mkulesh/stm32WindowSensor/images/screenschots/floor_1_alarm.png

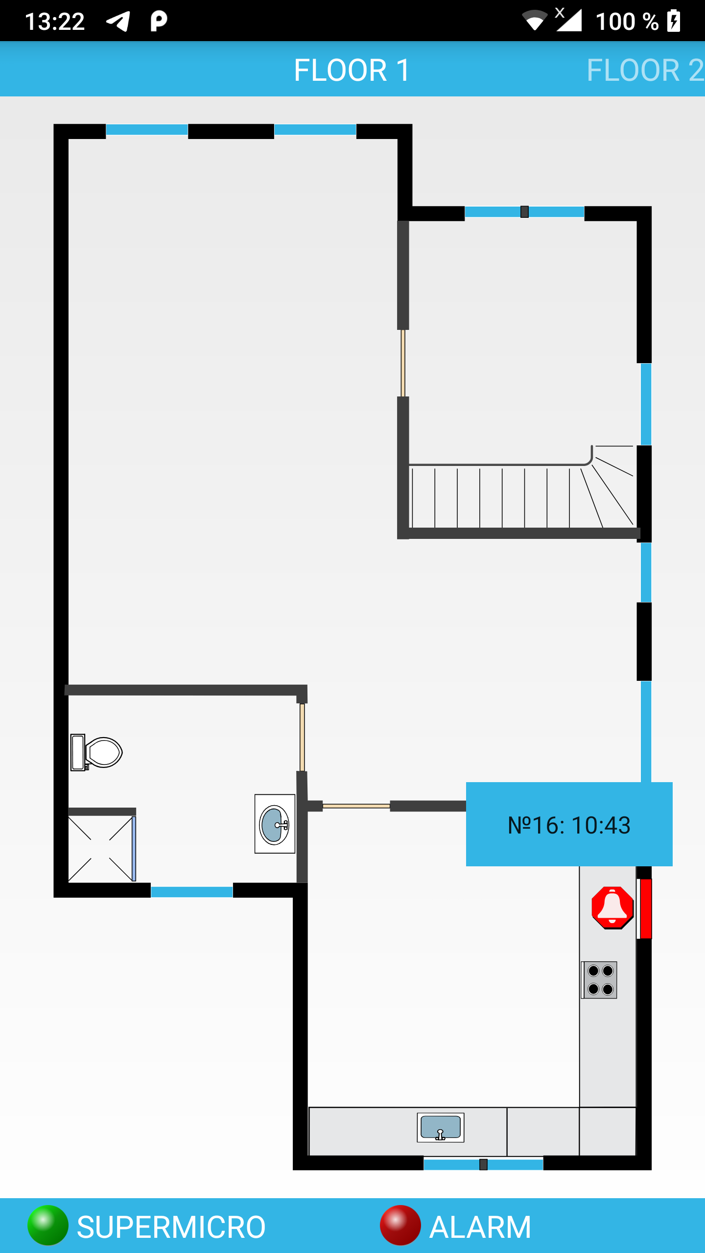
images/screenschots/floor_1_alarm.png
