mkulesh/stm32WindowSensor/images/screenschots/server.png

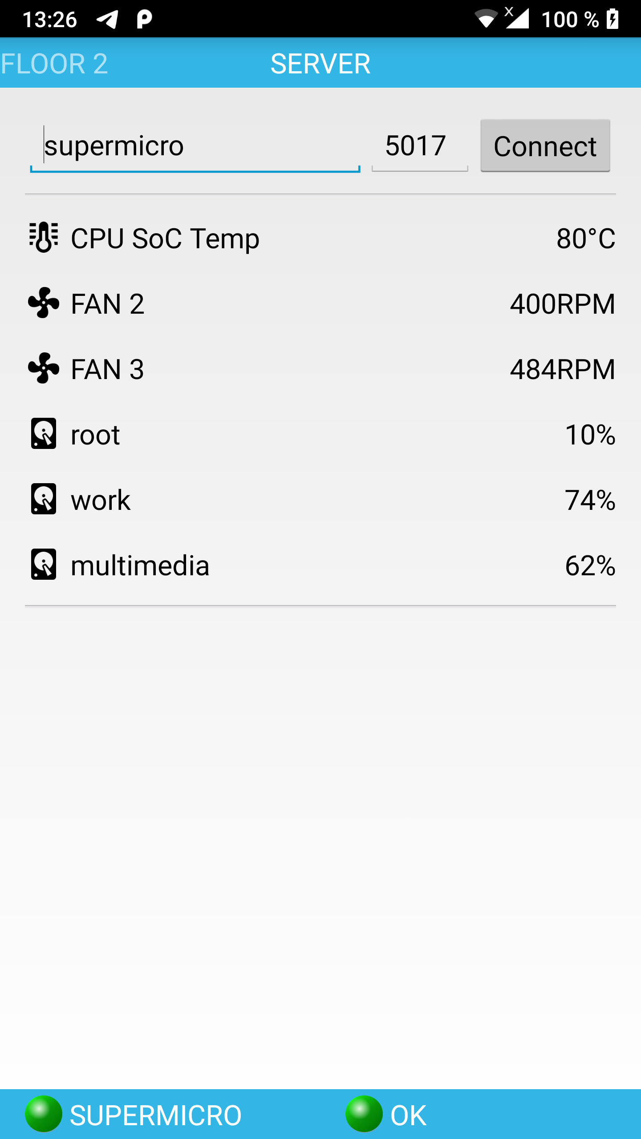
images/screenschots/server.png
