mkulesh/stm32WindowSensor/images/sensors/sensor06.jpg

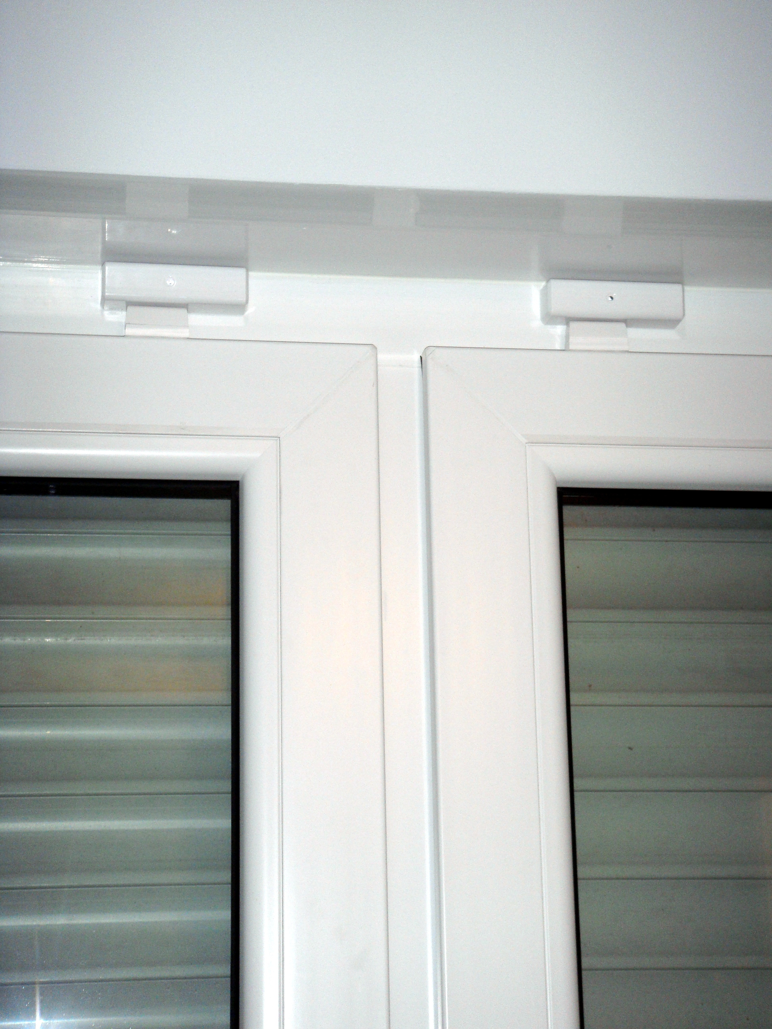
images/sensors/sensor06.jpg
