mkulesh/stm32WindowSensor/images/sensors/sensor08.jpg

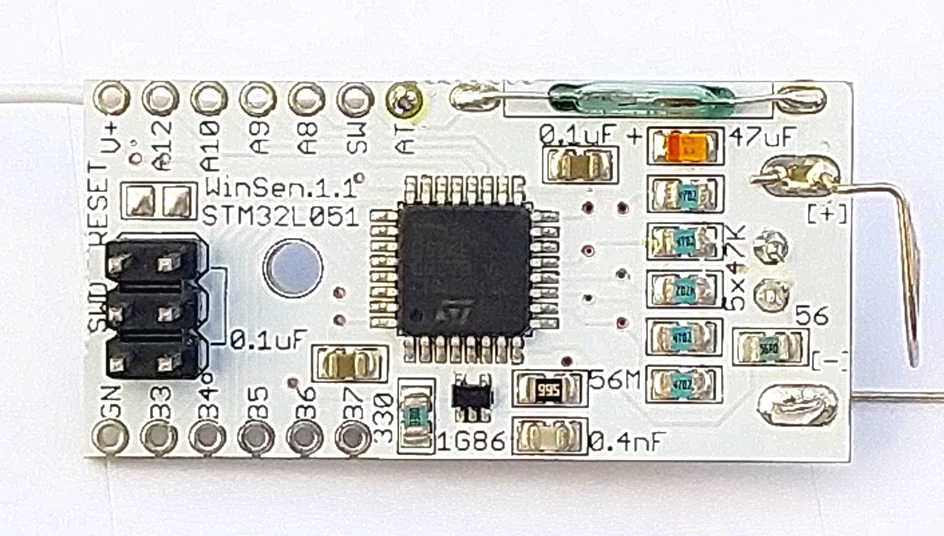
images/sensors/sensor08.jpg
