mkulesh/stm32WindowSensor/images/server/server01.jpg

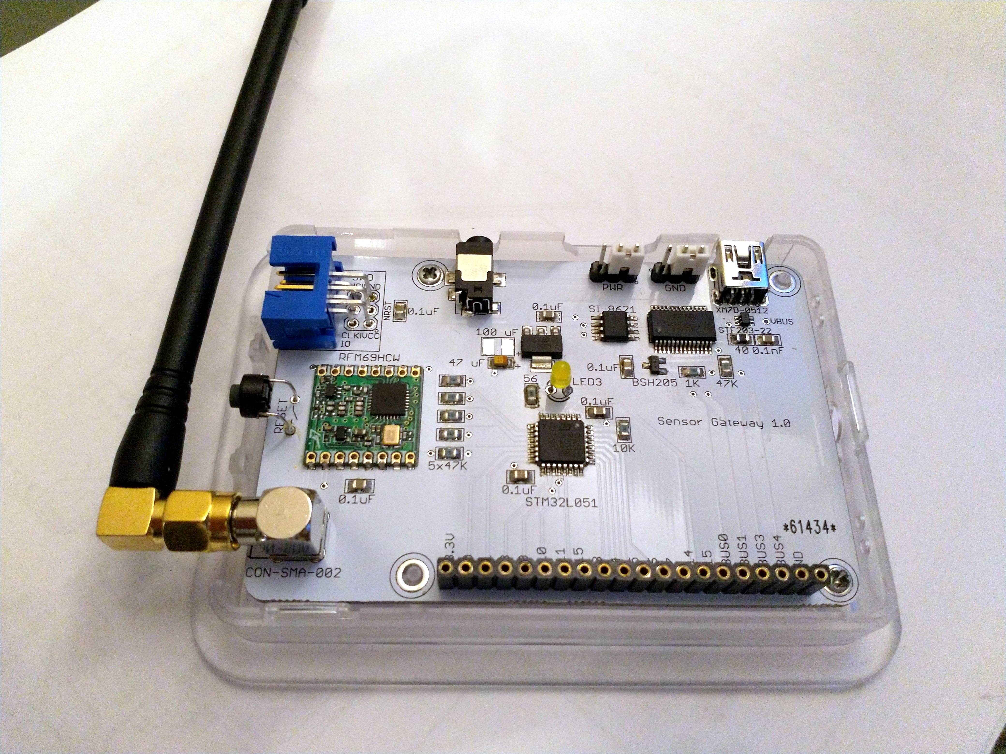
images/server/server01.jpg
